rdi-bj/ai-nas/ai-nas-software/src/web-ui/README.md

# src/web-ui/ — 管理界面

AI NAS 设备管理界面的前端源码（如状态查看、存储管理、AI 任务配置等）。以 **Mulan PSL v2** 许可发布。

> 如前端基于某上游框架 / 组件库构建，请在依赖清单与 NOTICE 中标注其许可，并补充 SBOM。
